LeanderU/KnockBox/software/Test_Submodules/secrets.py

# This file is where you keep secret settings, passwords, and tokens!
# If you put them in the code you risk committing that info or sharing it

secrets = {
    'ssid' : 'Pixel_Leander',
    'password' : '######',
    'timezone' : "America/Los_Angeles"
    }
